FOSSBOSS/SketchyEtch/v1_projectPics/knob.png

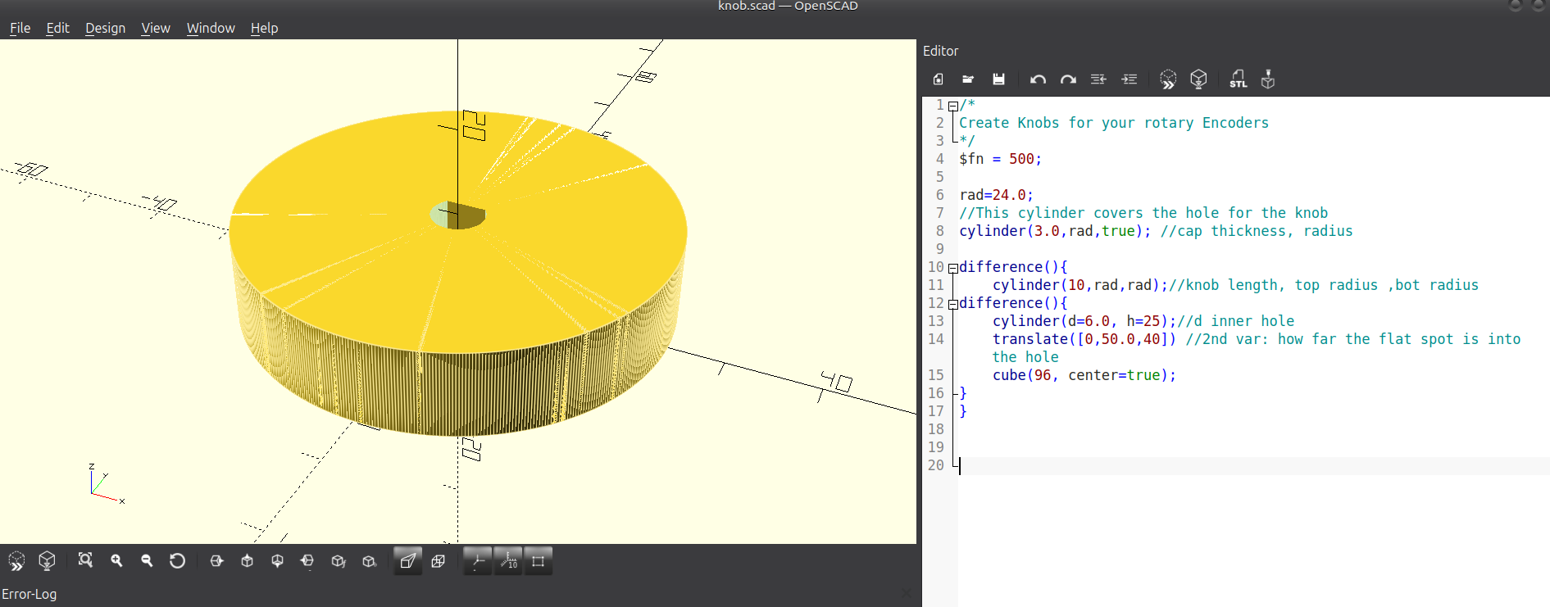
v1_projectPics/knob.png
