FOSSBOSS/SketchyEtch/v1_projectPics/play.jpg

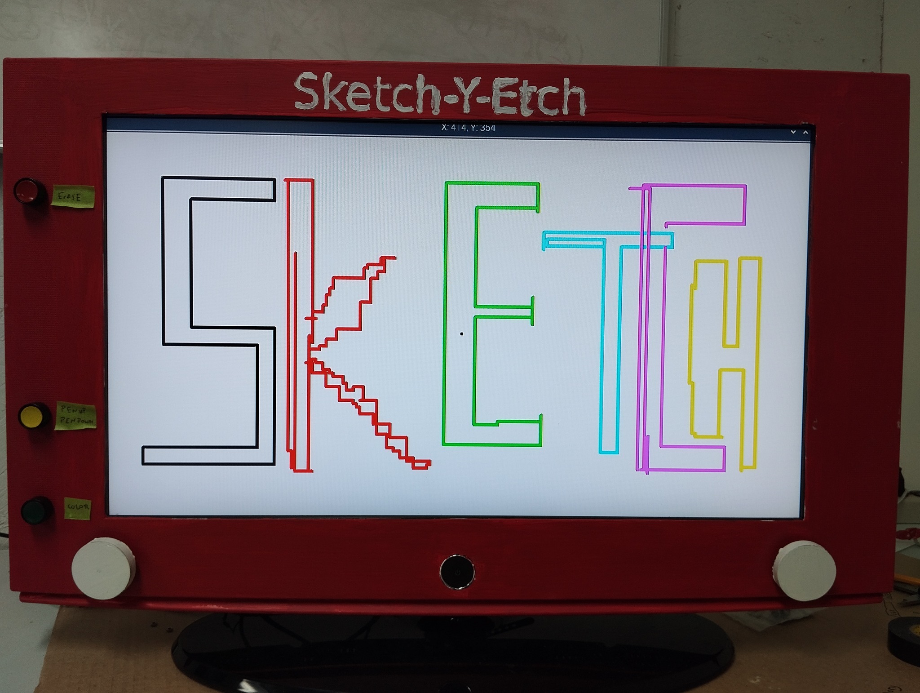
v1_projectPics/play.jpg
