FOSSBOSS/SketchyEtch/v1_projectPics/primed.jpg

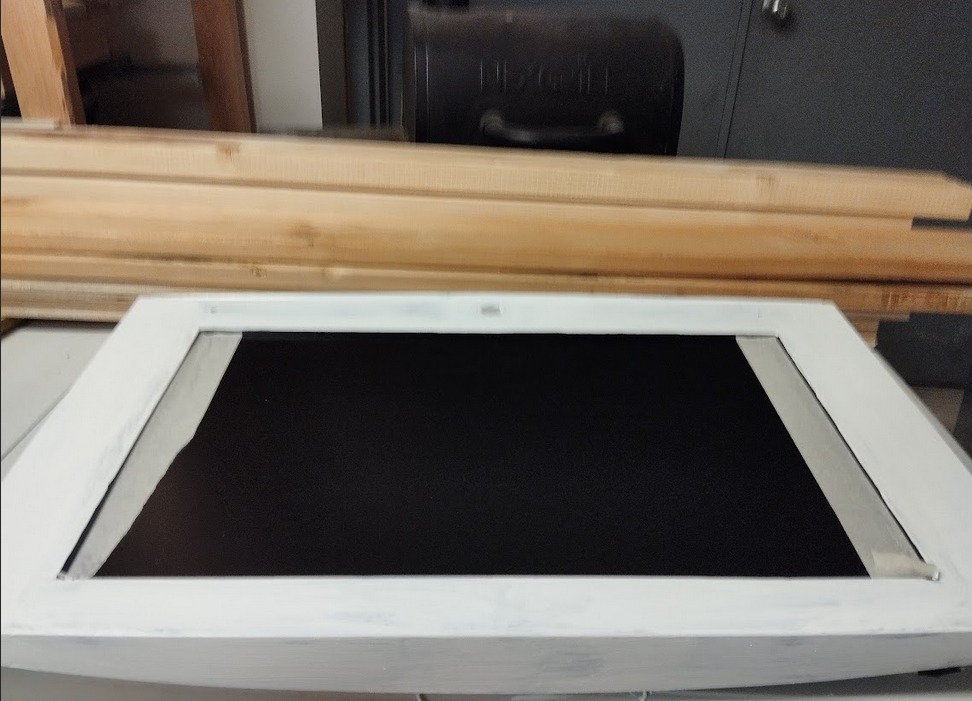
v1_projectPics/primed.jpg
