FOSSBOSS/SketchyEtch/v1_projectPics/v0_onlineEdition.png

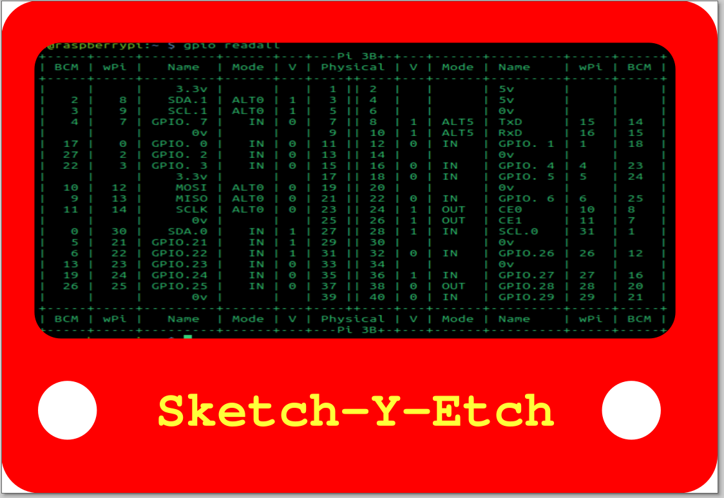
v1_projectPics/v0_onlineEdition.png
