FOSSBOSS/SketchyEtch/3D/tests/lego.scad

use <brick.scad>;
