FOSSBOSS/SketchyEtch/V2_WIP/images/Linux_busTesting.png

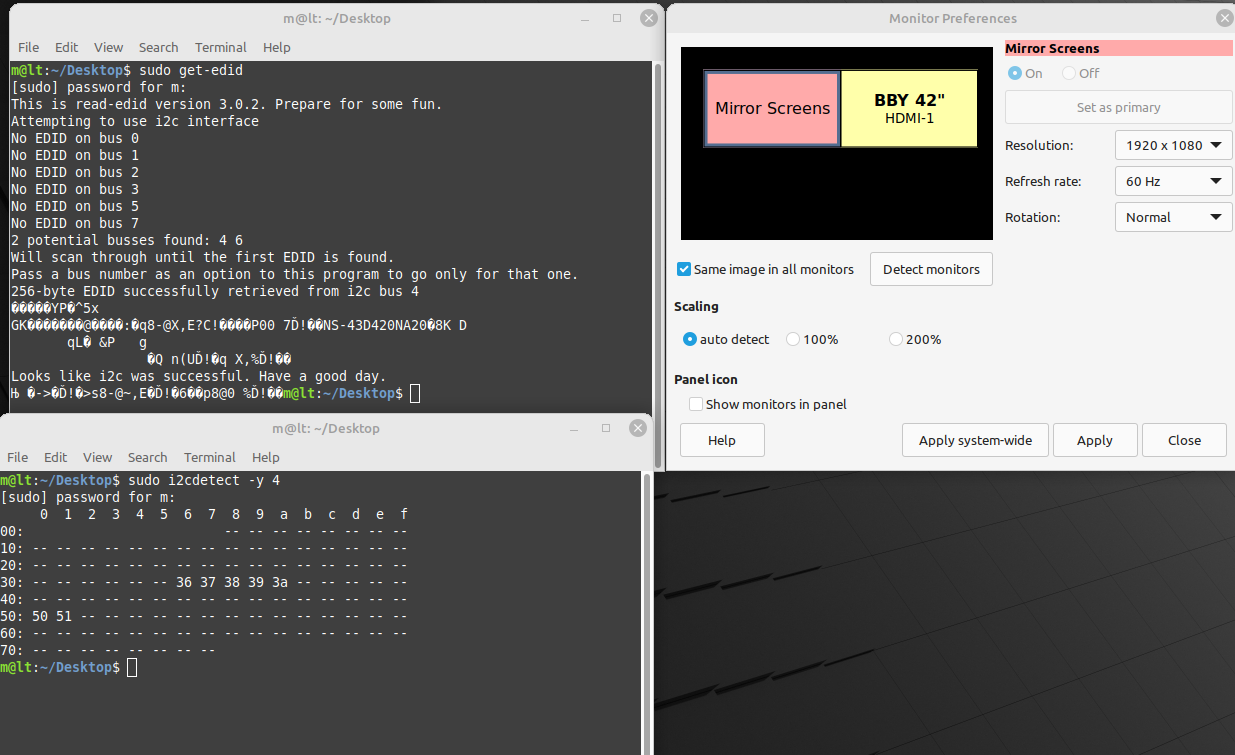
V2_WIP/images/Linux_busTesting.png
